Bhaskaryechuri/FishElectroreceptionCircuit/circuit.sch

## EAGLE design circuit.sch (2021-05-27)

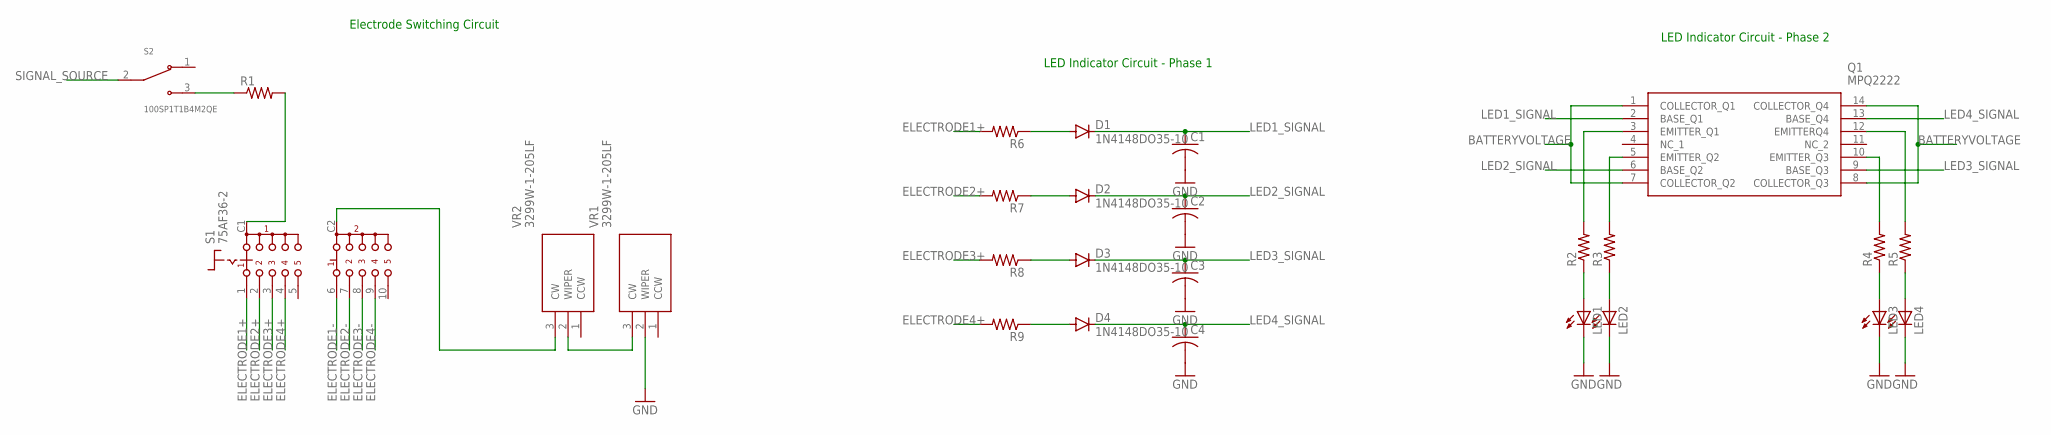
[picture p3: schematic circuit.sch]

Parts:
C1, C2, C3, C4: C-US025-024X044; C025-024X044
D1, D2, D3, D4: 1N4148DO35-10; DO35-10
LED1, LED2, LED3, LED4: LED5MM
Q1: MPQ2222; DIP890W60P250L1905H440Q14N
R1, R2, R3, R4, R5, R6, R7, R8, R9: R-US_0204/7; 0204/7
S1: 75AF36-2
S2: 100SP1T1B4M2QE; SW_100SP1T1B4M2QE
VR1, VR2: 3299W-1-205LF; 3299W-1-104LF_1

Connections:
BATTERYVOLTAGE: Q1.1 (COLLECTOR_Q1), Q1.8 (COLLECTOR_Q3), Q1.14 (COLLECTOR_Q4)
ELECTRODE1+: R6.2, S1.1 (11)
ELECTRODE1-: S1.6 (12)
ELECTRODE2+: R7.2, S1.2 (21)
ELECTRODE2-: S1.7 (22)
ELECTRODE3+: R8.2, S1.3 (31)
ELECTRODE3-: S1.8 (32)
ELECTRODE4+: R9.2, S1.4 (41)
ELECTRODE4-: S1.9 (42)
GND: C1.2, C2.2, C3.2, C4.2, LED1.K (C), LED2.K (C), LED3.K (C), LED4.K (C), VR1.2 (WIPER)
LED1_SIGNAL: C1.1, D1.C, Q1.2 (BASE_Q1)
LED2_SIGNAL: C2.1, D2.C, Q1.6 (BASE_Q2)
LED3_SIGNAL: C3.1, D3.C, Q1.9 (BASE_Q3)
LED4_SIGNAL: C4.1, D4.C, Q1.13 (BASE_Q4)
unnamed: R1.1, S2.3
unnamed: R1.2, S1.C1
unnamed: S1.C2, VR2.3 (CW)
unnamed: VR1.3 (CW), VR2.2 (WIPER)
unnamed: Q1.3 (EMITTER_Q1), R2.2
unnamed: Q1.5 (EMITTER_Q2), R3.2
unnamed: Q1.12 (EMITTERQ4), R5.2
unnamed: Q1.10 (EMITTER_Q3), R4.2
unnamed: LED1.A, R2.1
unnamed: LED2.A, R3.1
unnamed: LED3.A, R4.1
unnamed: LED4.A, R5.1
unnamed: D1.A, R6.1
unnamed: D2.A, R7.1
unnamed: D3.A, R8.1
unnamed: D4.A, R9.1
SIGNAL_SOURCE: S2.2

Notes on the sheet:
Electrode Switching Circuit
LED Indicator Circuit - Phase 2
LED Indicator Circuit - Phase 1
